OUTOFDARTSSHOP/Rival-Juno-Blaster/Juno v5/Juno-Accent_V5.2.3mf

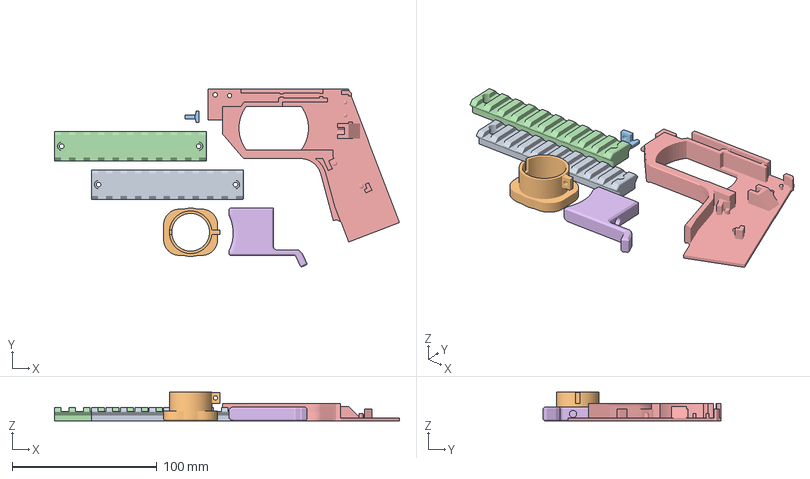
[picture p17: CAD file, 2023-12-07]
Juno v5/Juno-Accent_V5.2.3mf
238.4 x 122.9 x 19.7 mm
f85b52f7-413b-456e-a1ac-1456022f8551.stl_1
f85b52f7-413b-456e-a1ac-1456022f8551.stl_2
f85b52f7-413b-456e-a1ac-1456022f8551.stl_13
f85b52f7-413b-456e-a1ac-1456022f8551.stl_19
Juno-HandleInner_V5.1.stl
Juno-Trigger_V5.2.stl
