OUTOFDARTSSHOP/Rival-Juno-Blaster/Juno v5/STLs/Handle/Juno-HandleInner_V5.1.stl

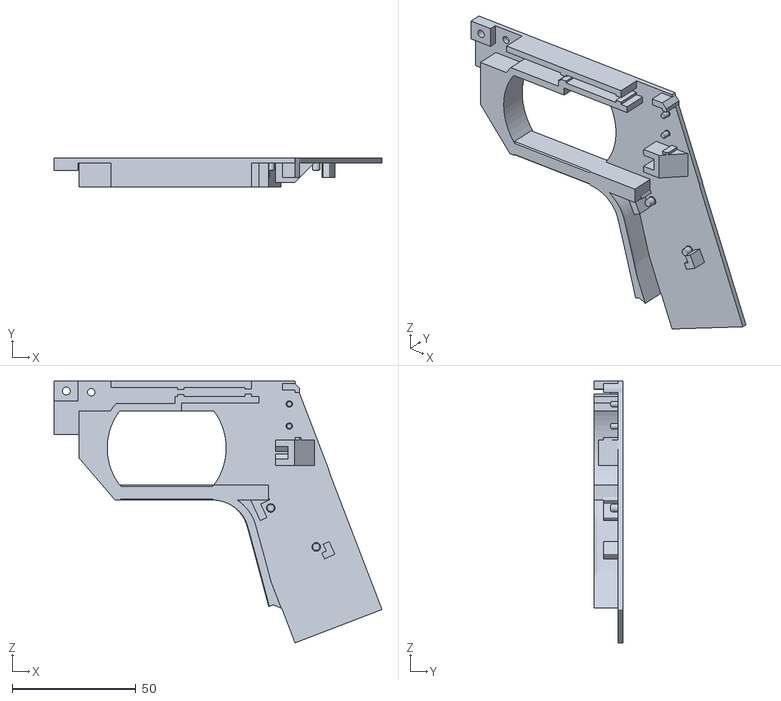
[picture p18: CAD file, 2023-12-05]
Juno v5/STLs/Handle/Juno-HandleInner_V5.1.stl
132.4 x 11.8 x 105.7
