OUTOFDARTSSHOP/Rival-Juno-Blaster/PPAdapter v2/PPAdapter-Swivel_V2.stl

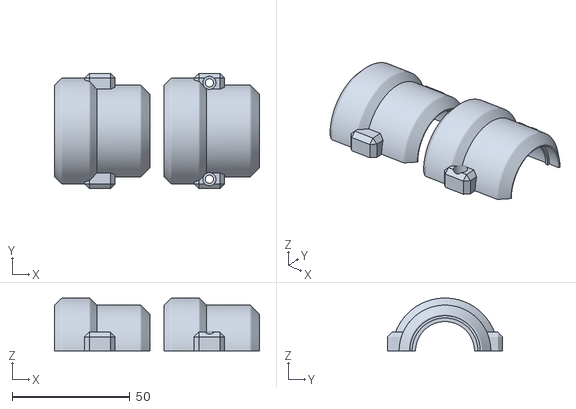
[picture p19: CAD file, 2023-11-28]
PPAdapter v2/PPAdapter-Swivel_V2.stl
87.2 x 49.0 x 22.5
