OUTOFDARTSSHOP/Rival-Juno-Blaster/Juno v5/Archieve/Juno-HandleInner_V5.stl

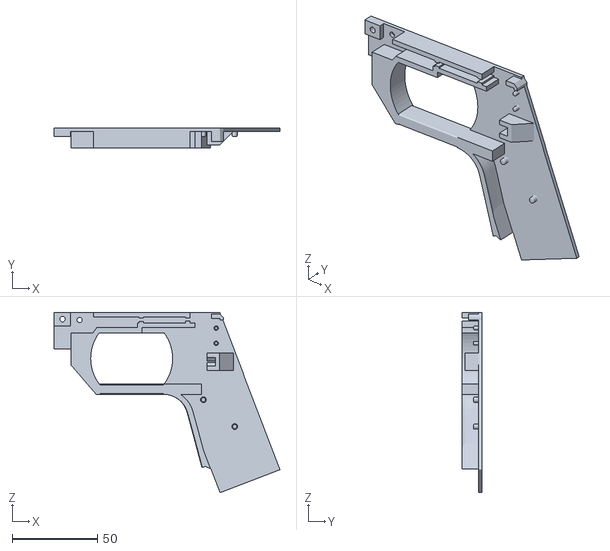
[picture p20: CAD file, 2023-11-24]
Juno v5/Archieve/Juno-HandleInner_V5.stl
132.4 x 11.8 x 105.7
