OUTOFDARTSSHOP/Rival-Juno-Blaster/Juno v5/Juno-Primary_V5.3mf

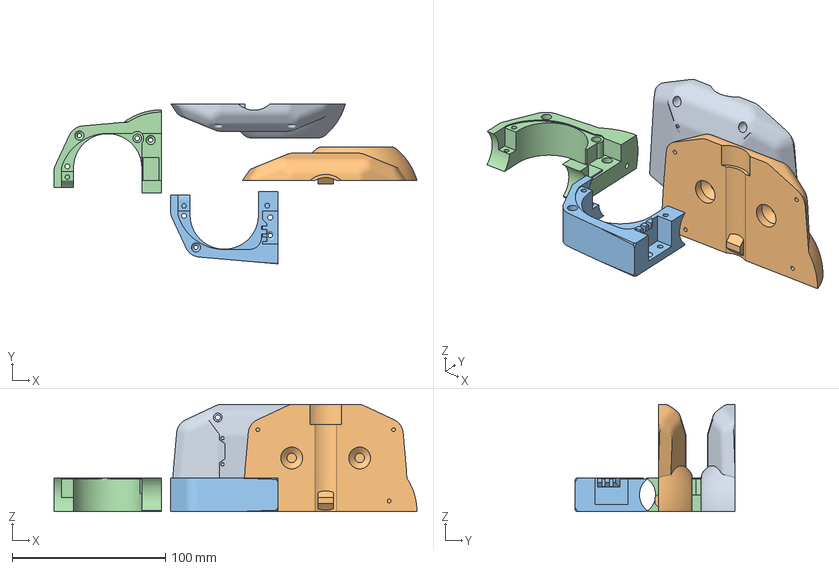
[picture p21: CAD file, 2023-11-24]
Juno v5/Juno-Primary_V5.3mf
236.6 x 104.2 x 70.0 mm
f85b52f7-413b-456e-a1ac-1456022f8551.stl_3
f85b52f7-413b-456e-a1ac-1456022f8551.stl_8
f85b52f7-413b-456e-a1ac-1456022f8551.stl_9
f85b52f7-413b-456e-a1ac-1456022f8551.stl_12
