OUTOFDARTSSHOP/Rival-Juno-Blaster/Juno v5/STLs/Front/Juno-Pusher Casing_V5.1.stl

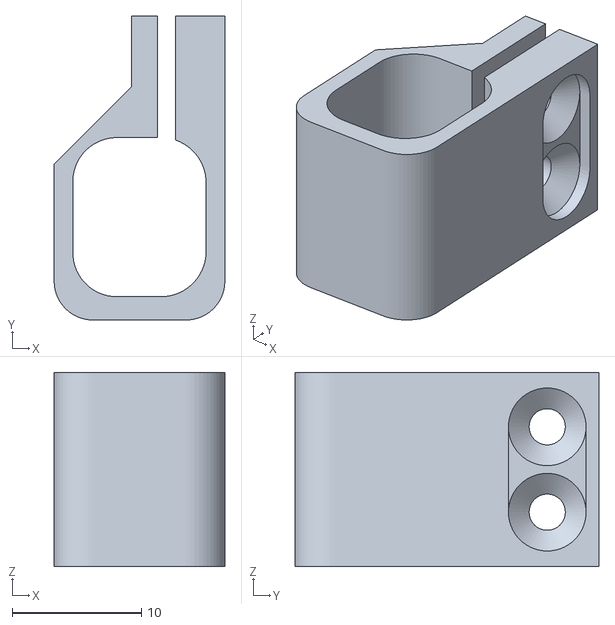
[picture p22: CAD file, 2023-12-05]
Juno v5/STLs/Front/Juno-Pusher Casing_V5.1.stl
13.2 x 23.5 x 15.0
