OUTOFDARTSSHOP/Rival-Juno-Blaster/Juno v5/STLs/Handle/Juno-SlingPoint_V5.stl

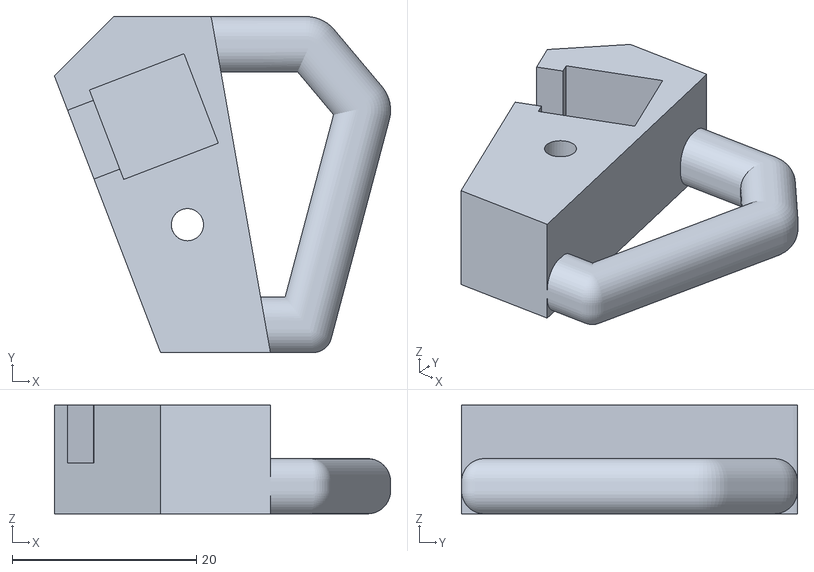
[picture p23: CAD file, 2023-11-28]
Juno v5/STLs/Handle/Juno-SlingPoint_V5.stl
36.5 x 36.5 x 11.8
