OUTOFDARTSSHOP/Rival-Juno-Blaster/Juno v5/STLs/Mag-Battery/Juno-Cover-Pict_V5.stl

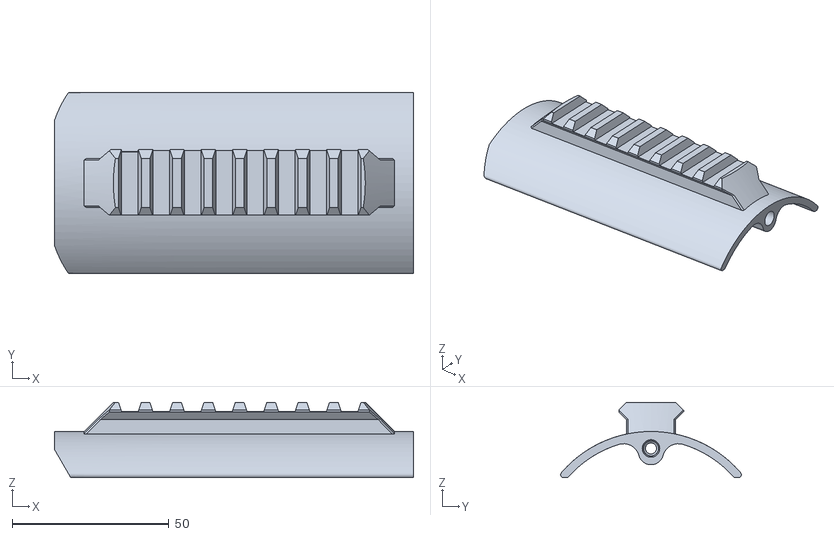
[picture p24: CAD file, 2023-11-24]
Juno v5/STLs/Mag-Battery/Juno-Cover-Pict_V5.stl
114.4 x 57.6 x 24.1
