OUTOFDARTSSHOP/Rival-Juno-Blaster/PPAdapter v2/PPAdapter-Backplate_V2.stl

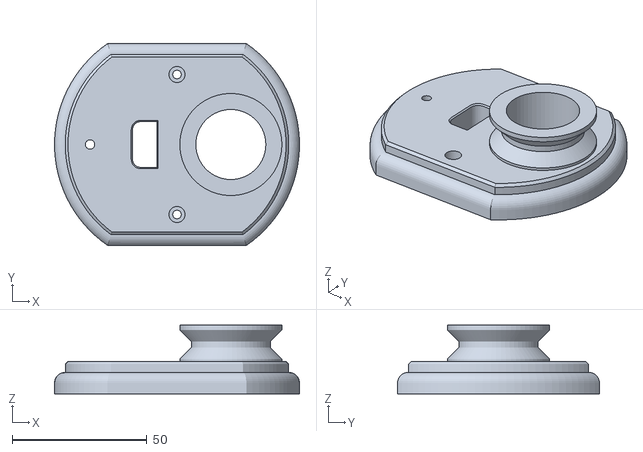
[picture p25: CAD file, 2023-11-28]
PPAdapter v2/PPAdapter-Backplate_V2.stl
91.0 x 75.0 x 25.5
