OUTOFDARTSSHOP/Rival-Juno-Blaster/Juno v5/Juno-Primary-Mag-Battery_V5.3mf

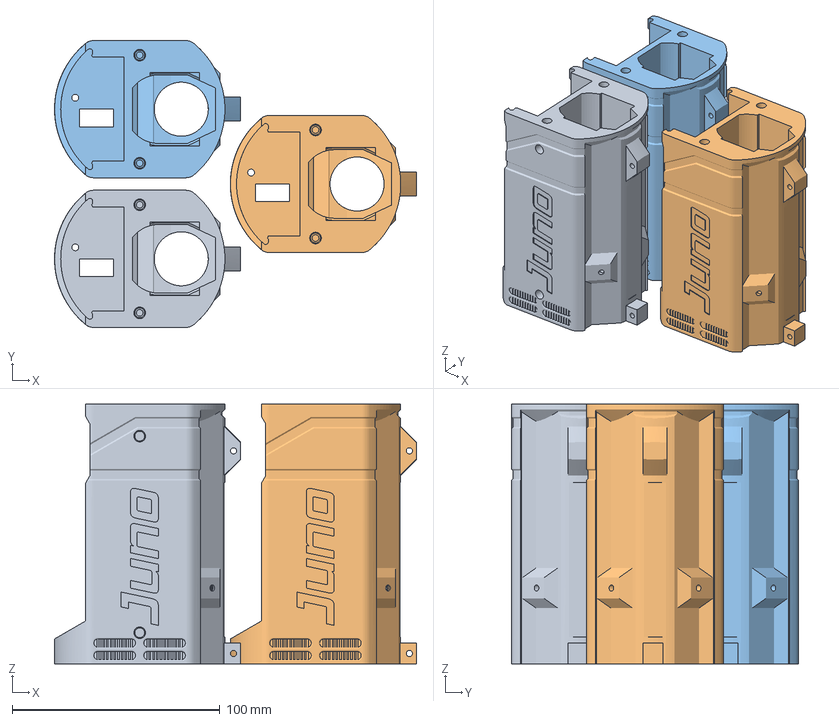
[picture p26: CAD file, 2023-11-24]
Juno v5/Juno-Primary-Mag-Battery_V5.3mf
174.2 x 138.0 x 125.0 mm
f85b52f7-413b-456e-a1ac-1456022f8551.stl_16
f85b52f7-413b-456e-a1ac-1456022f8551.stl_17
f85b52f7-413b-456e-a1ac-1456022f8551.stl_18
