OUTOFDARTSSHOP/Rival-Juno-Blaster/Juno v5/Archieve/Juno-Pusher Casing_V5.stl

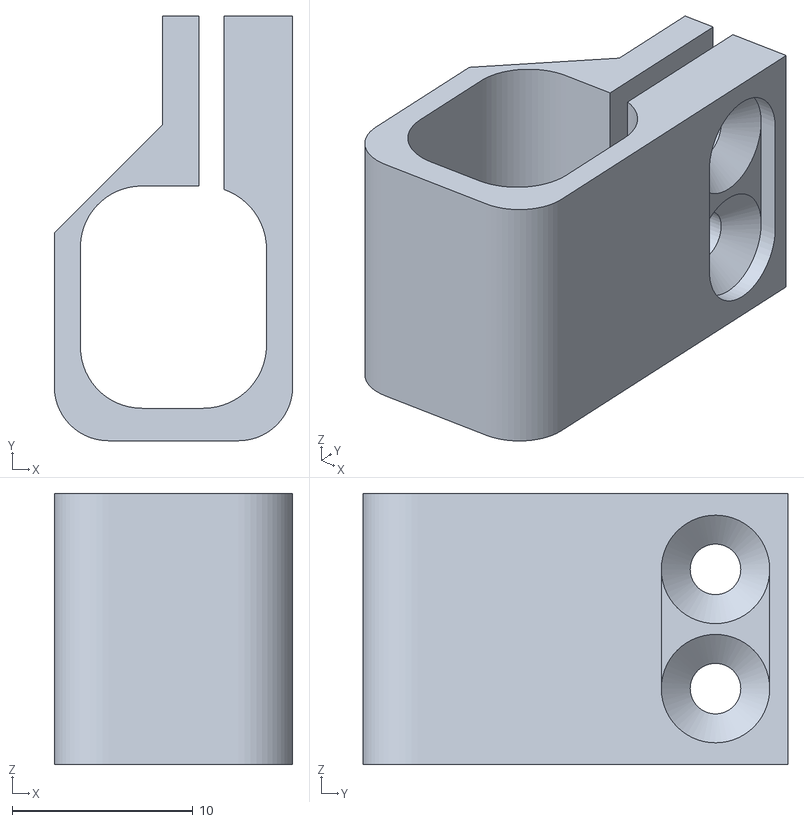
[picture p27: CAD file, 2023-11-24]
Juno v5/Archieve/Juno-Pusher Casing_V5.stl
13.2 x 23.5 x 15.0
