OUTOFDARTSSHOP/Rival-Juno-Blaster/Juno v5/Juno-Accent-BatteryTray_V5.3mf

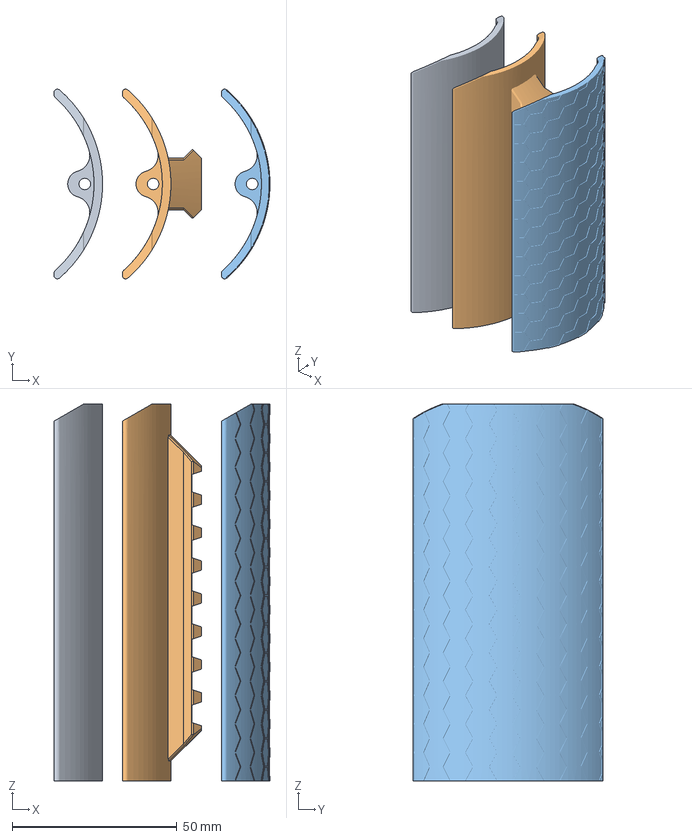
[picture p28: CAD file, 2023-11-24]
Juno v5/Juno-Accent-BatteryTray_V5.3mf
65.5 x 57.6 x 114.4 mm
f85b52f7-413b-456e-a1ac-1456022f8551.stl_20
f85b52f7-413b-456e-a1ac-1456022f8551.stl_21
f85b52f7-413b-456e-a1ac-1456022f8551.stl_22
