OUTOFDARTSSHOP/Rival-Juno-Blaster/Juno v5/Archieve/Juno-Trigger_V5.stl

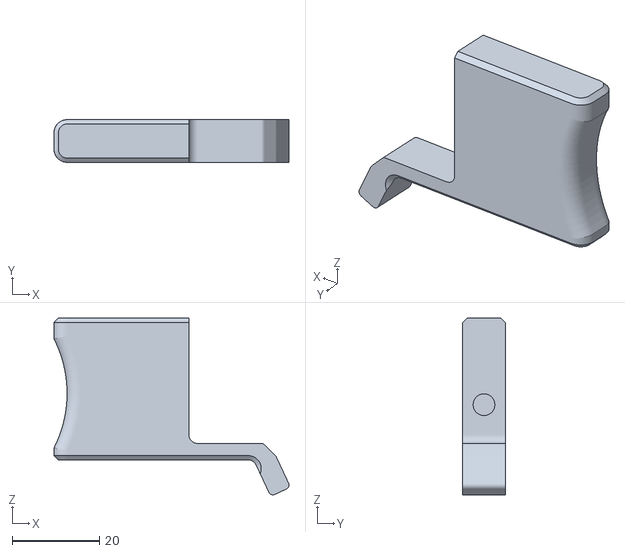
[picture p29: CAD file, 2023-11-24]
Juno v5/Archieve/Juno-Trigger_V5.stl
54.0 x 9.80 x 40.6
