OUTOFDARTSSHOP/Rival-Juno-Blaster/Juno v5/STLs/Front/Juno-Left Plate_V5.stl

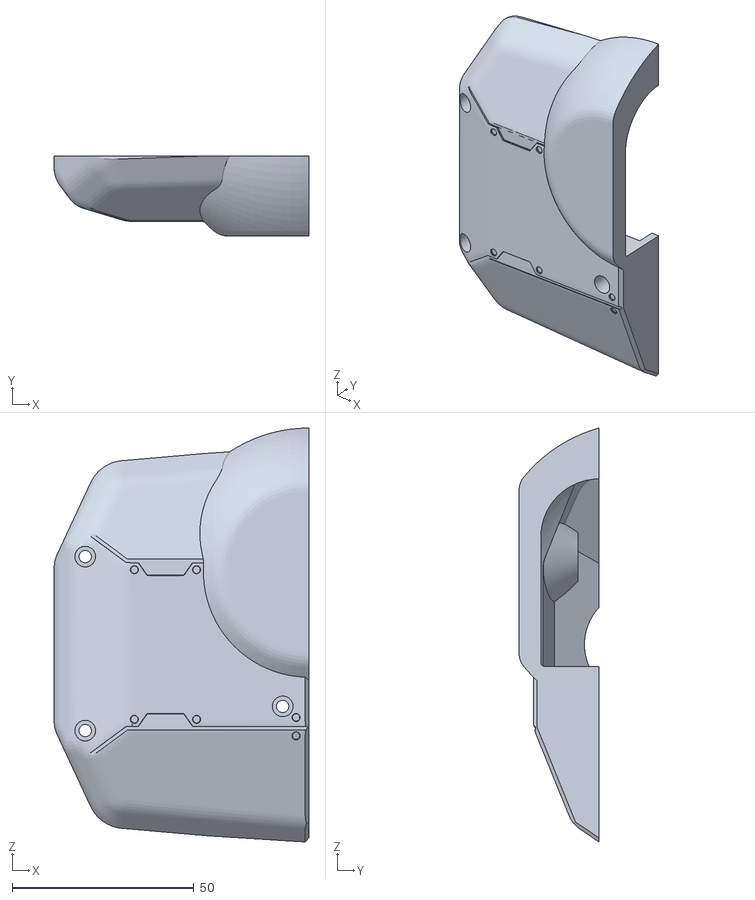
[picture p30: CAD file, 2023-11-24]
Juno v5/STLs/Front/Juno-Left Plate_V5.stl
70.0 x 22.0 x 113.8
