OUTOFDARTSSHOP/Rival-Juno-Blaster/Juno v5/STLs/Mag-Battery/Juno-Back Cap_V5.stl

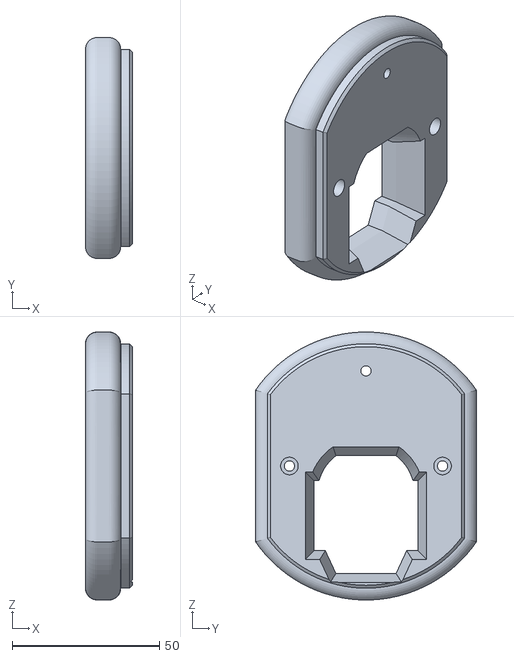
[picture p31: CAD file, 2023-11-24]
Juno v5/STLs/Mag-Battery/Juno-Back Cap_V5.stl
16.0 x 75.0 x 91.0
