OUTOFDARTSSHOP/Rival-Juno-Blaster/Juno v5/Archieve/Juno-Accent_V5.3mf

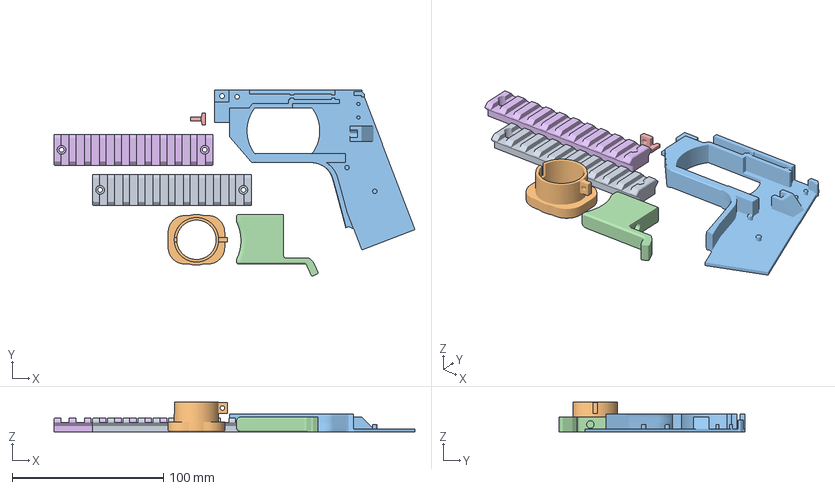
[picture p32: CAD file, 2023-11-24]
Juno v5/Archieve/Juno-Accent_V5.3mf
238.4 x 122.9 x 19.7 mm
f85b52f7-413b-456e-a1ac-1456022f8551.stl_1
f85b52f7-413b-456e-a1ac-1456022f8551.stl_2
f85b52f7-413b-456e-a1ac-1456022f8551.stl_5
f85b52f7-413b-456e-a1ac-1456022f8551.stl_7
f85b52f7-413b-456e-a1ac-1456022f8551.stl_13
f85b52f7-413b-456e-a1ac-1456022f8551.stl_19
