OUTOFDARTSSHOP/Rival-Juno-Blaster/Juno v5/STLs/Front/Juno-RightPlate_V5.stl

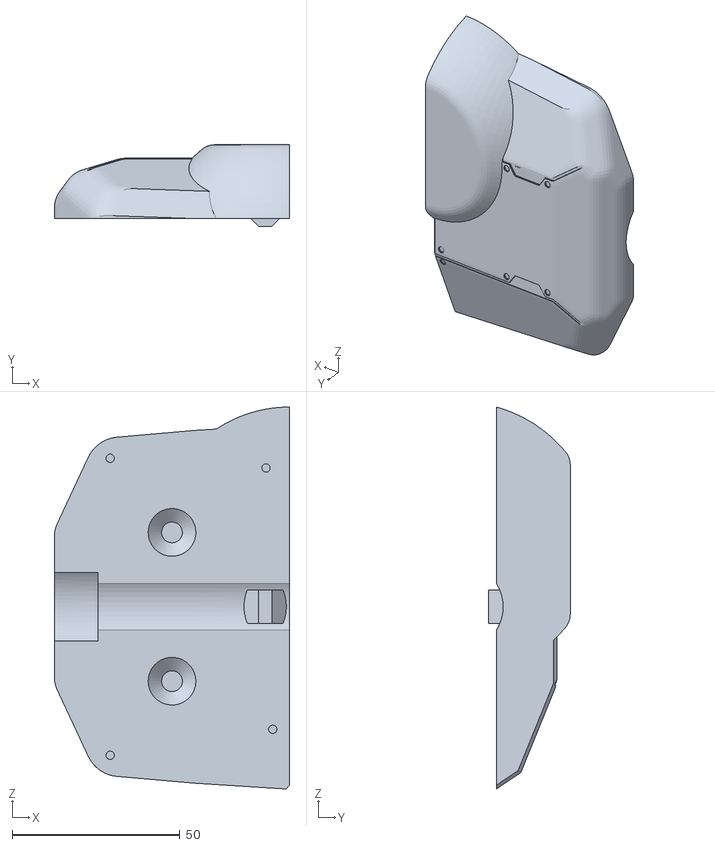
[picture p34: CAD file, 2023-11-24]
Juno v5/STLs/Front/Juno-RightPlate_V5.stl
70.0 x 24.3 x 113.8
