OUTOFDARTSSHOP/Rival-Juno-Blaster/Juno v5/STLs/Front/Juno-Bottom Center_V5.stl

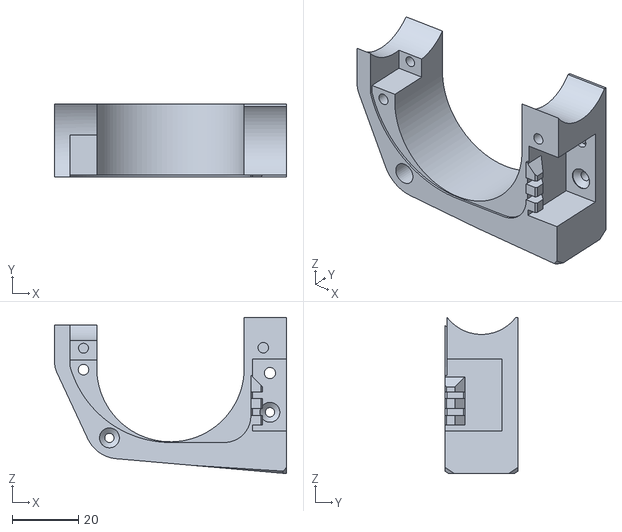
[picture p35: CAD file, 2023-11-24]
Juno v5/STLs/Front/Juno-Bottom Center_V5.stl
70.0 x 22.0 x 47.1
